tyler-l-thompson/SailCam/3D_Objects/panel_mount/section_4.stl

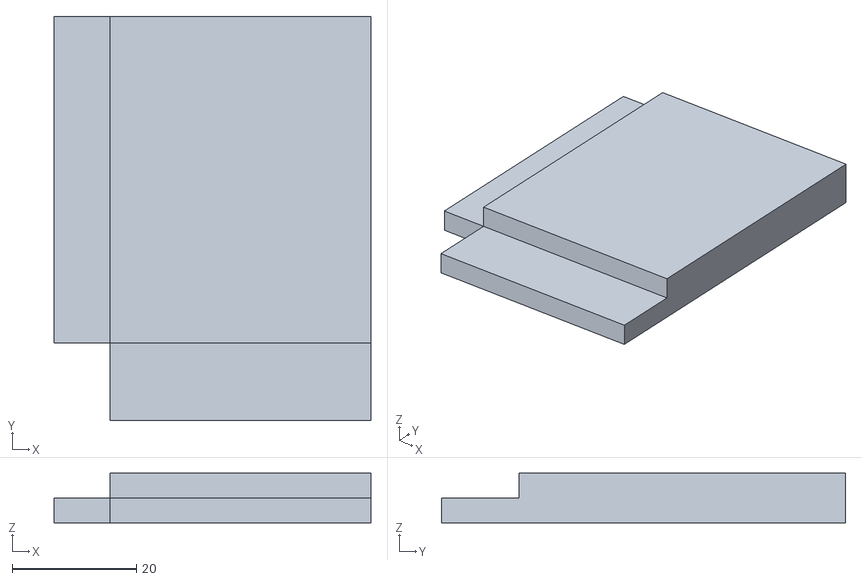
[picture p23: CAD file, 2019-07-10]
3D_Objects/panel_mount/section_4.stl
51.0 x 65.0 x 8.00
