tyler-l-thompson/SailCam/3D_Objects/SailCam_MK5/SailCamMK5_BoatCase_Top.stl

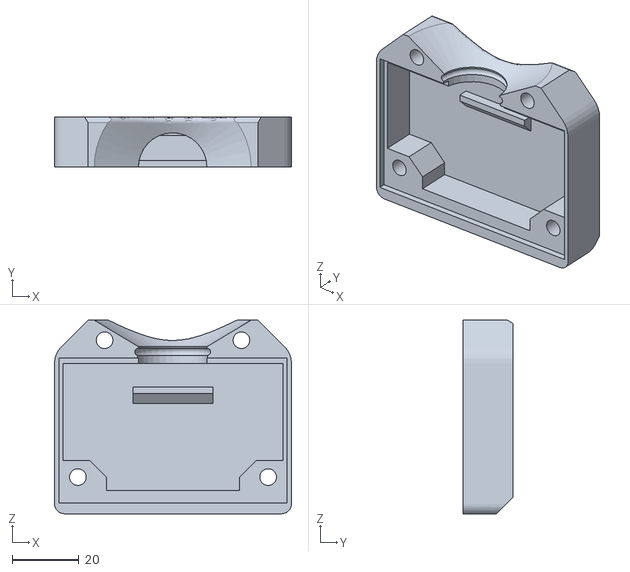
[picture p24: CAD file, 2022-08-22]
3D_Objects/SailCam_MK5/SailCamMK5_BoatCase_Top.stl
71.0 x 15.0 x 58.0
