tyler-l-thompson/SailCam/3D_Objects/stand_bracket_post.stl

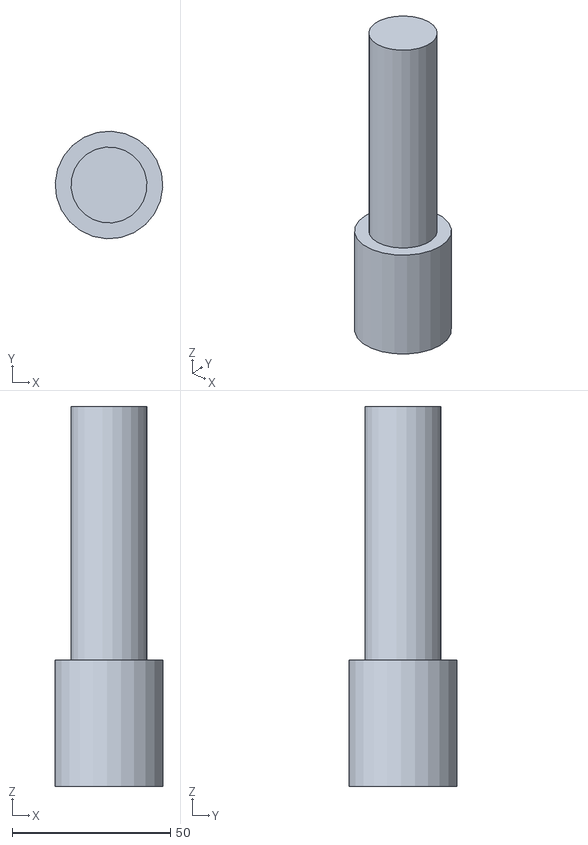
[picture p25: CAD file, 2019-07-10]
3D_Objects/stand_bracket_post.stl
34.0 x 34.0 x 120.0
