tyler-l-thompson/SailCam/3D_Objects/bracket_top.stl

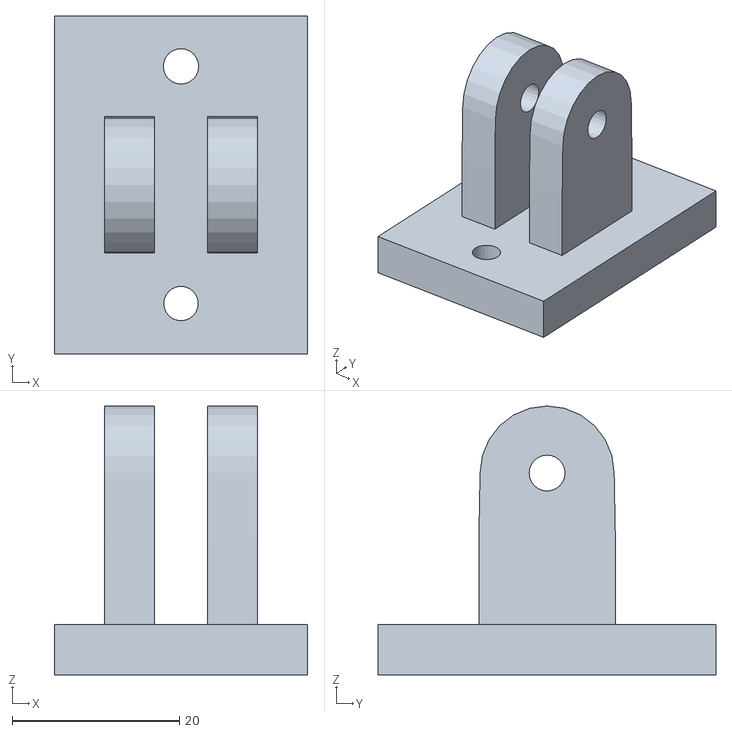
[picture p26: CAD file, 2019-07-10]
3D_Objects/bracket_top.stl
30.3 x 40.4 x 32.2
