tyler-l-thompson/SailCam/3D_Objects/SailCam_MK5/SailCamMK5_BasicCaseV2_Front.stl

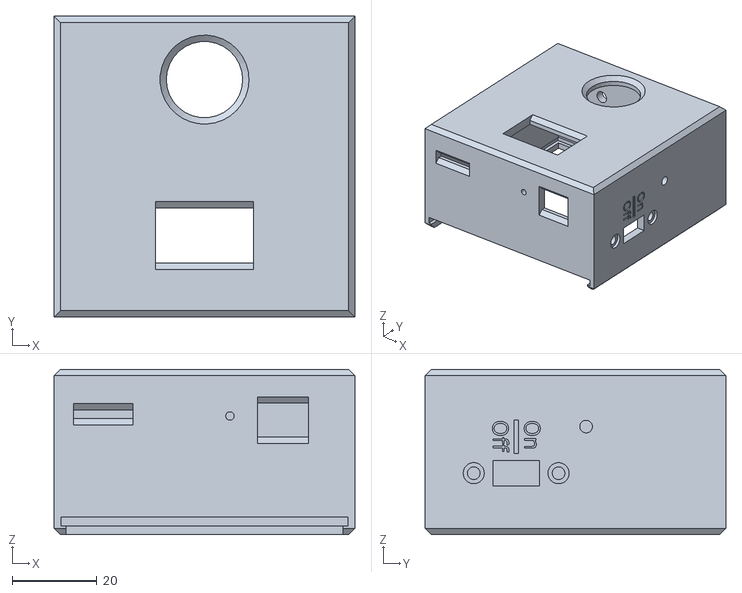
[picture p27: CAD file, 2022-01-05]
3D_Objects/SailCam_MK5/SailCamMK5_BasicCaseV2_Front.stl
71.0 x 71.0 x 39.0
