tyler-l-thompson/SailCam/3D_Objects/bracket_bottom.stl

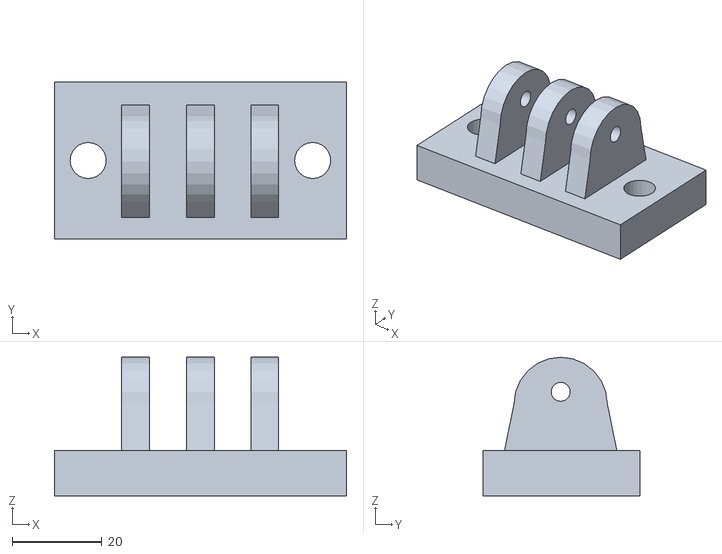
[picture p28: CAD file, 2019-07-10]
3D_Objects/bracket_bottom.stl
64.9 x 35.0 x 30.8
