tyler-l-thompson/SailCam/3D_Objects/SailCam_MK5/SailCamMK5_BoatCase_ClampBracket.stl

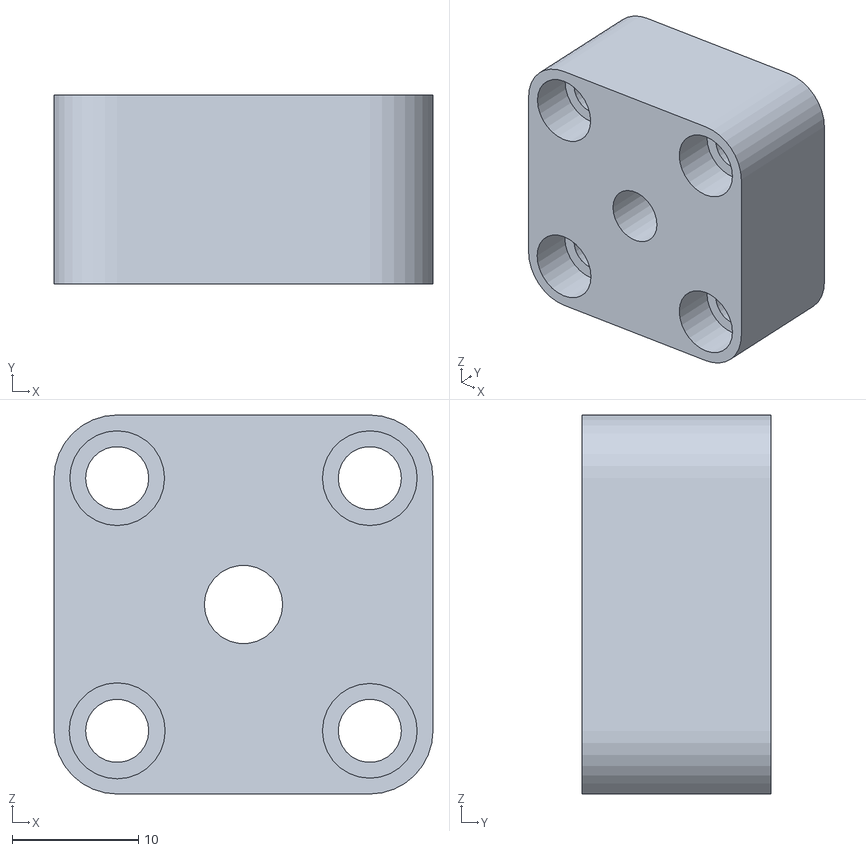
[picture p29: CAD file, 2021-09-20]
3D_Objects/SailCam_MK5/SailCamMK5_BoatCase_ClampBracket.stl
30.0 x 15.0 x 30.0
