tyler-l-thompson/SailCam/3D_Objects/SailCam_MK5/SailCamMK5_BasicCaseV2_Back.stl

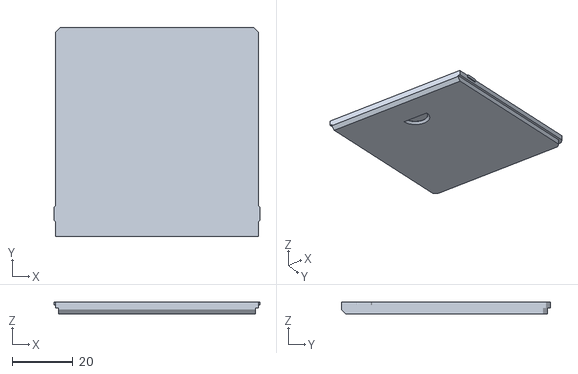
[picture p30: CAD file, 2021-09-20]
3D_Objects/SailCam_MK5/SailCamMK5_BasicCaseV2_Back.stl
68.0 x 69.0 x 4.00
