tyler-l-thompson/SailCam/3D_Objects/SailCam_MK5/RubberGaskey_20mm.step

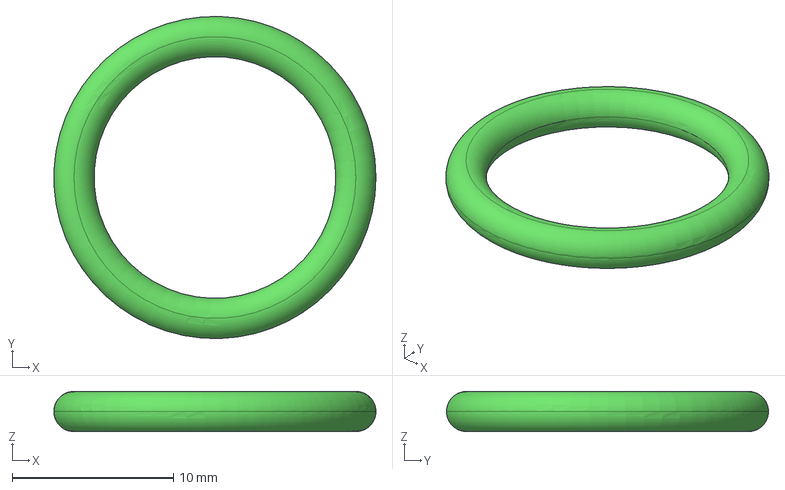
[picture p31: CAD file, 2021-08-21]
3D_Objects/SailCam_MK5/RubberGaskey_20mm.step
20.0 x 20.0 x 2.50 mm
