tyler-l-thompson/SailCam/3D_Objects/SailCam_MK5/AAA Batterie.step

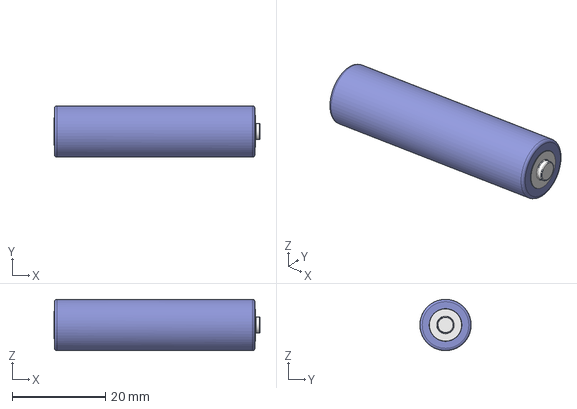
[picture p32: CAD file, 2021-08-21]
3D_Objects/SailCam_MK5/AAA Batterie.step
44.2 x 11.0 x 11.0 mm
