tyler-l-thompson/SailCam/3D_Objects/SailCam_MK5/Clamp.step

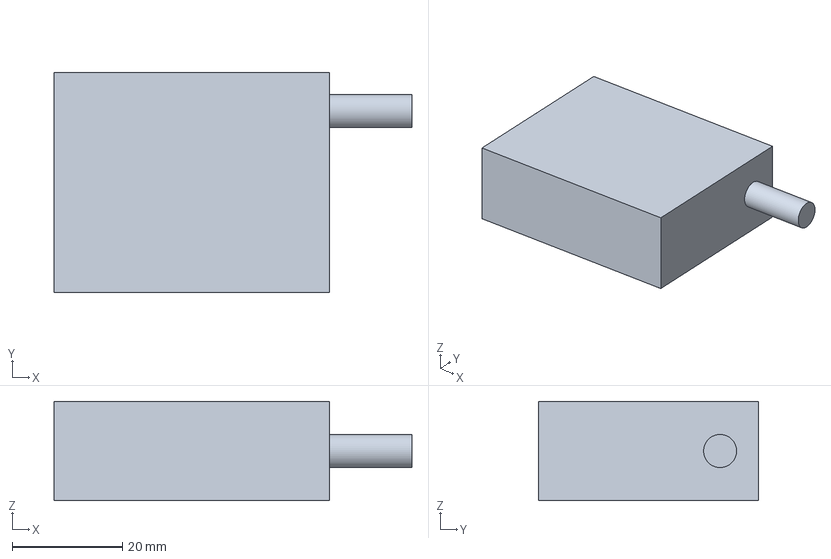
[picture p33: CAD file, 2021-08-21]
3D_Objects/SailCam_MK5/Clamp.step
65.0 x 40.0 x 18.0 mm
