tyler-l-thompson/SailCam/3D_Objects/SailCam_MK5/SailCamMK5_BasicCase_Front.stl

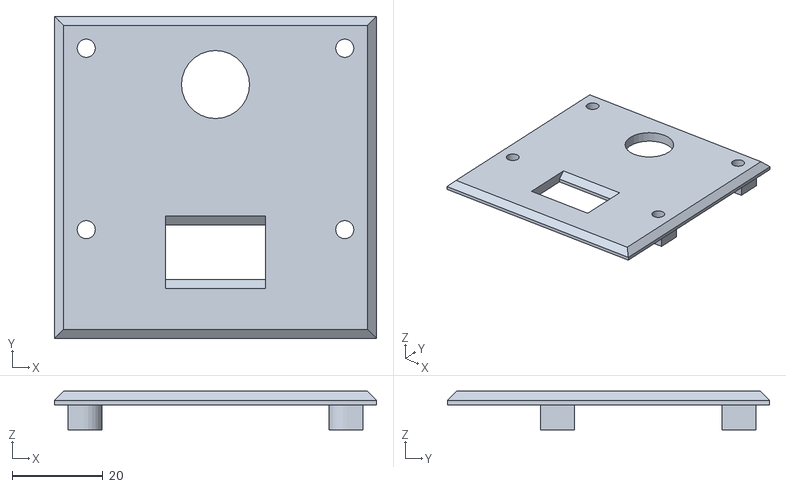
[picture p34: CAD file, 2021-08-21]
3D_Objects/SailCam_MK5/SailCamMK5_BasicCase_Front.stl
71.0 x 71.0 x 8.50
