tyler-l-thompson/SailCam/3D_Objects/SailCam_MK5/Button.step

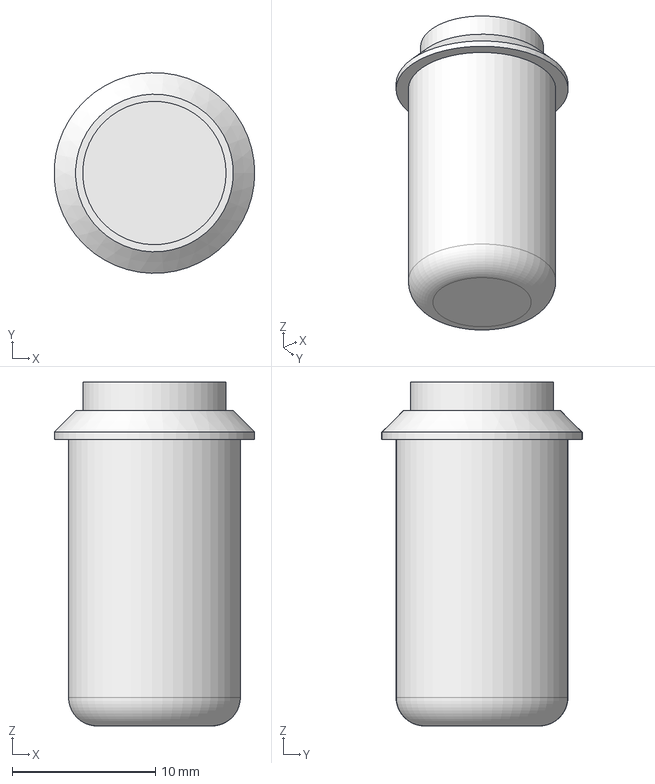
[picture p35: CAD file, 2021-08-21]
3D_Objects/SailCam_MK5/Button.step
14.0 x 14.0 x 24.0 mm
