tyler-l-thompson/SailCam/3D_Objects/SailCam_MK5/USB - Type B - Male - 90°.STEP

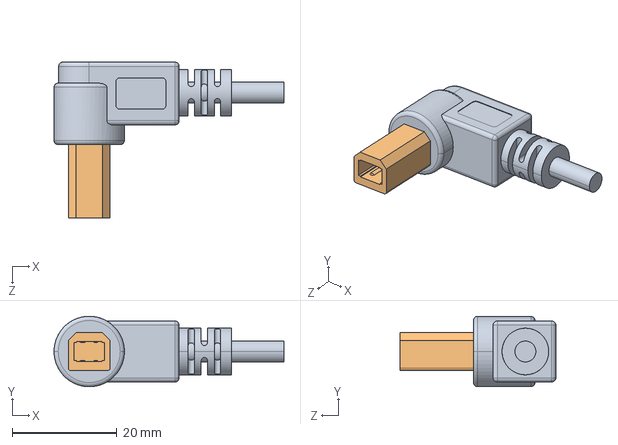
[picture p36: CAD file, 2021-08-21]
3D_Objects/SailCam_MK5/USB - Type B - Male - 90°.STEP
43.9 x 13.5 x 29.8 mm
