tyler-l-thompson/SailCam/3D_Objects/SailCam_MK5/usb_cable.stp

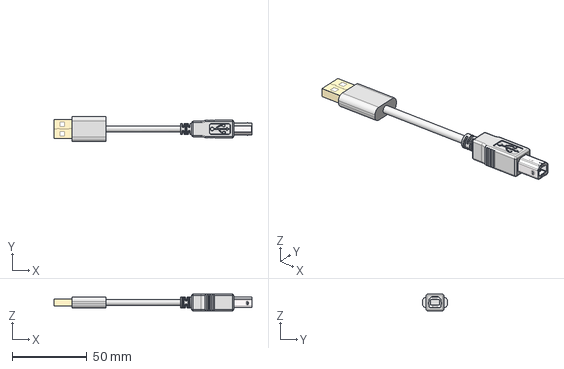
[picture p37: CAD file, 2021-08-21]
3D_Objects/SailCam_MK5/usb_cable.stp
132.6 x 17.0 x 11.2 mm
