tyler-l-thompson/SailCam/3D_Objects/SailCam_MK5/SailCamMK5_BasicCase_Back.stl

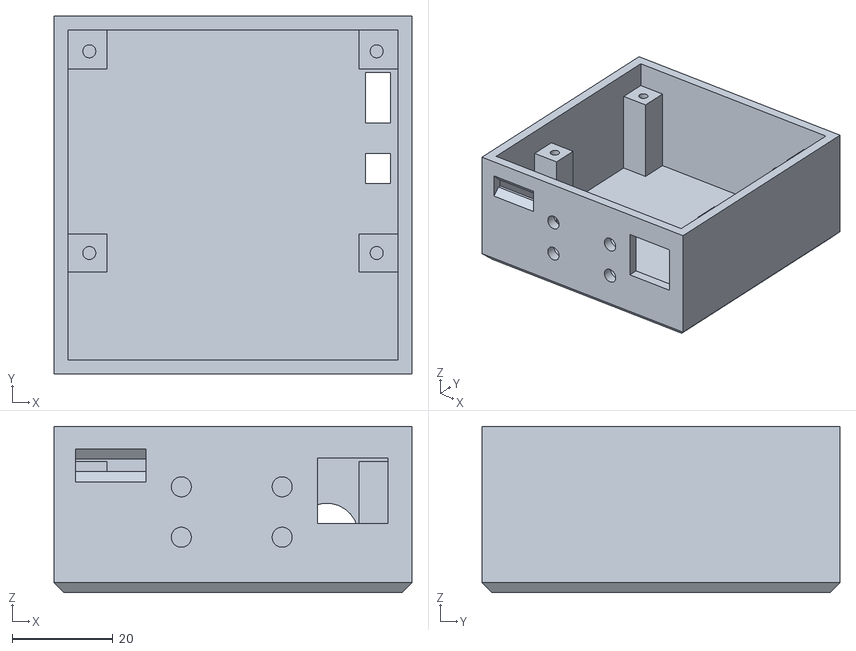
[picture p38: CAD file, 2021-08-21]
3D_Objects/SailCam_MK5/SailCamMK5_BasicCase_Back.stl
71.0 x 71.0 x 33.0
