tyler-l-thompson/SailCam/3D_Objects/SailCam_MK5/PowerConnector.step

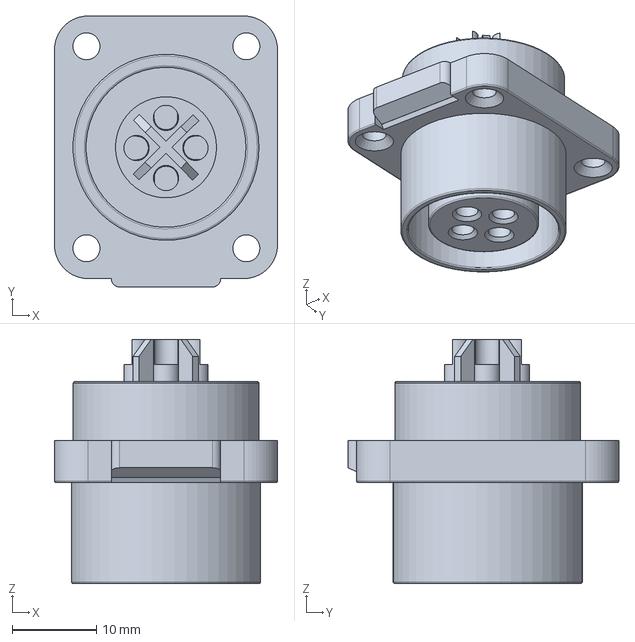
[picture p39: CAD file, 2021-08-21]
3D_Objects/SailCam_MK5/PowerConnector.step
26.5 x 32.2 x 29.0 mm
